dh219/DFB/wiki_resources/dead_socket.jpg

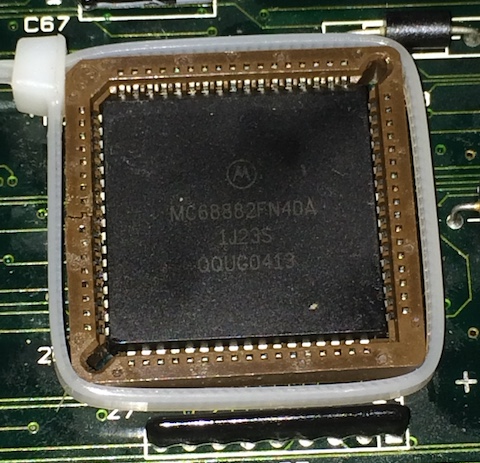
wiki_resources/dead_socket.jpg
