dh219/DFB/wiki_resources/DFB1r3_working.jpeg

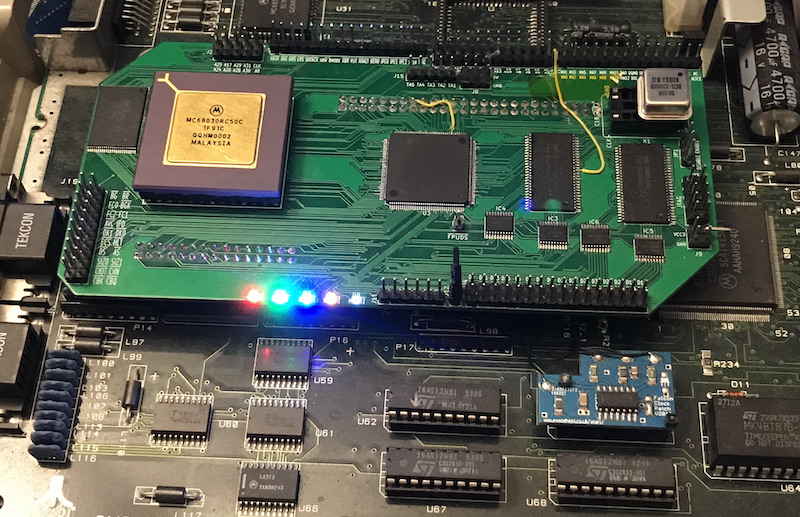
wiki_resources/DFB1r3_working.jpeg
