dh219/DFB/wiki_resources/DFB_memory.png

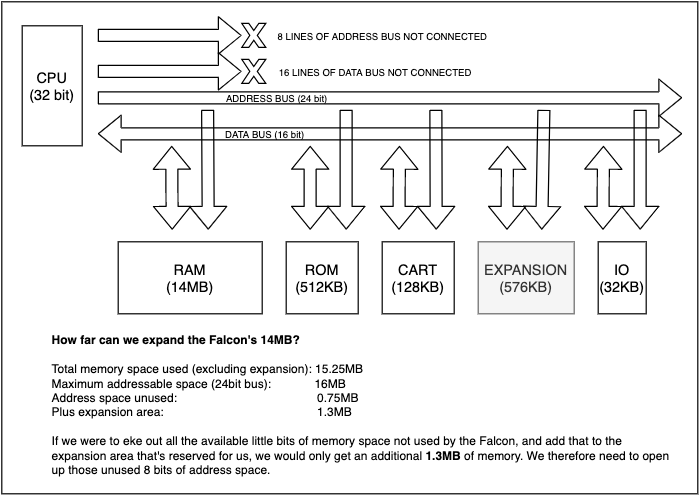
wiki_resources/DFB_memory.png
