dh219/DFB/wiki_resources/diag_cart_signs_of_life.jpeg

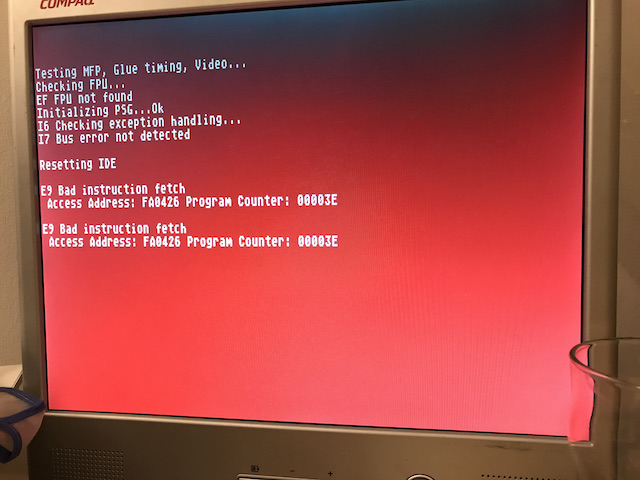
wiki_resources/diag_cart_signs_of_life.jpeg
