dh219/DFB/wiki_resources/DSACK0_stock.jpeg

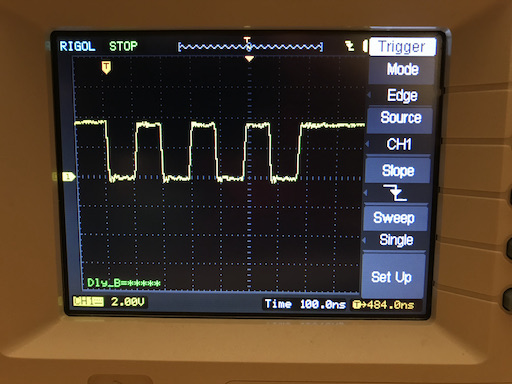
wiki_resources/DSACK0_stock.jpeg
