dh219/DFB/wiki_resources/DSP_access_native.png

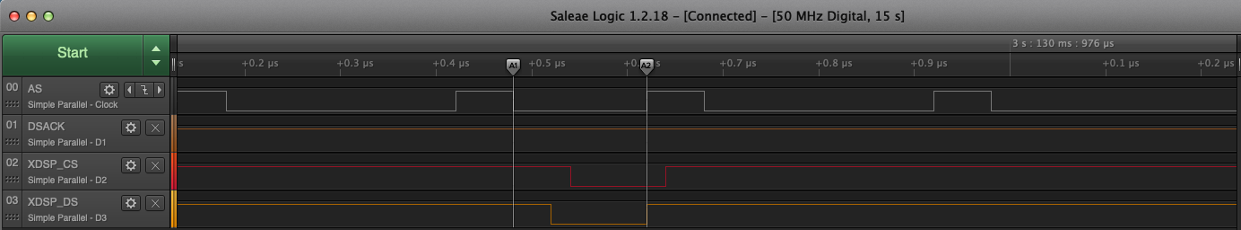
wiki_resources/DSP_access_native.png
