dh219/DFB/wiki_resources/fpu_hack.jpeg

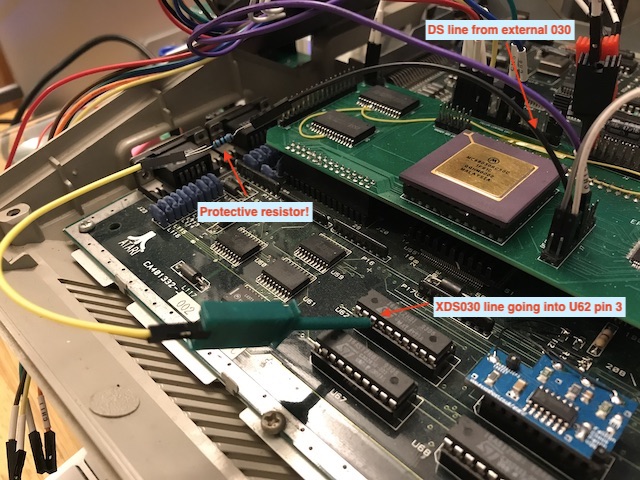
wiki_resources/fpu_hack.jpeg
