dh219/DFB/wiki_resources/rev1.jpeg

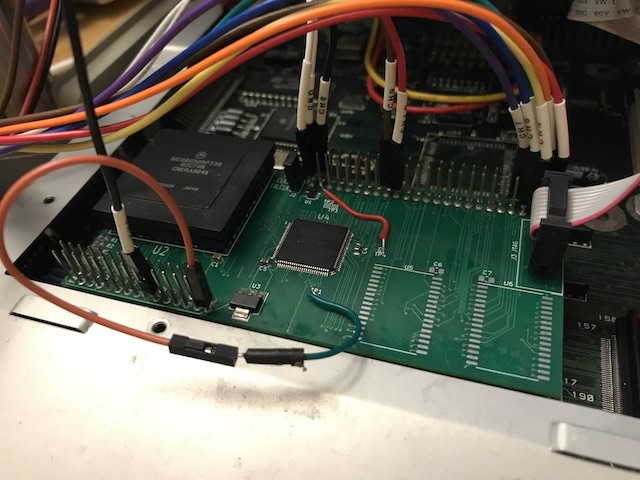
wiki_resources/rev1.jpeg
