dh219/DFB/wiki_resources/rev1_ram.jpeg

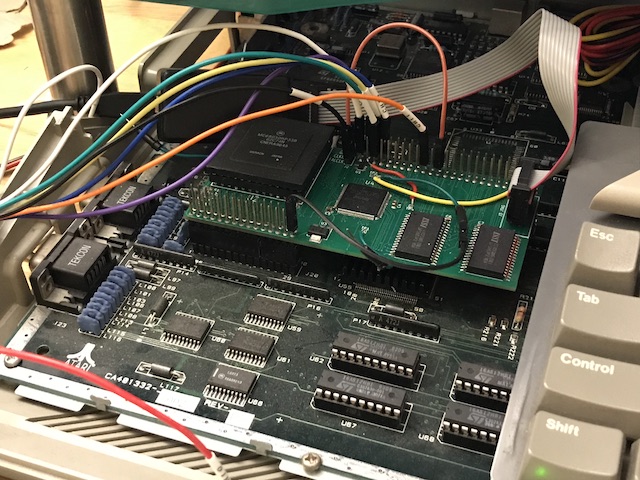
wiki_resources/rev1_ram.jpeg
