dh219/DFB/wiki_resources/rev2.jpeg

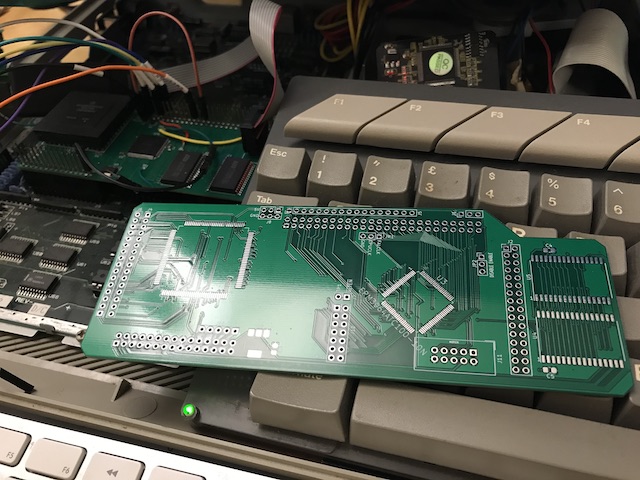
wiki_resources/rev2.jpeg
