dh219/DFB/wiki_resources/rev2b_noram.jpeg

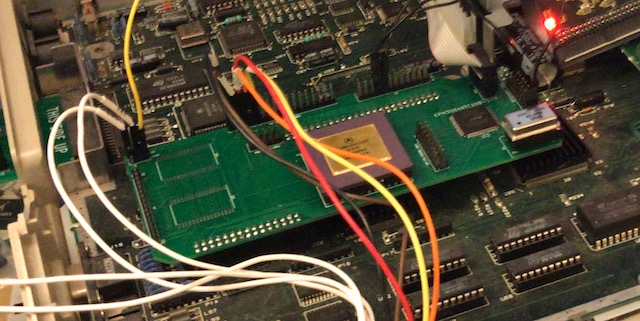
wiki_resources/rev2b_noram.jpeg
