dh219/DFB/wiki_resources/rev2b_ram.jpeg

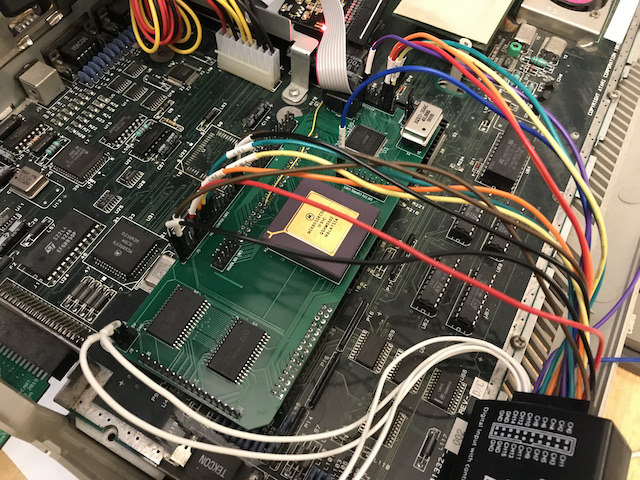
wiki_resources/rev2b_ram.jpeg
