dh219/DFB/wiki_resources/U62.png

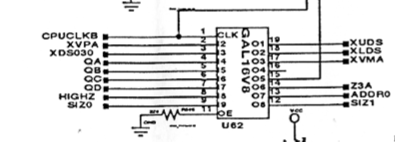
wiki_resources/U62.png
