dh219/DFB/wiki_resources/DSP_access_board_problem.png

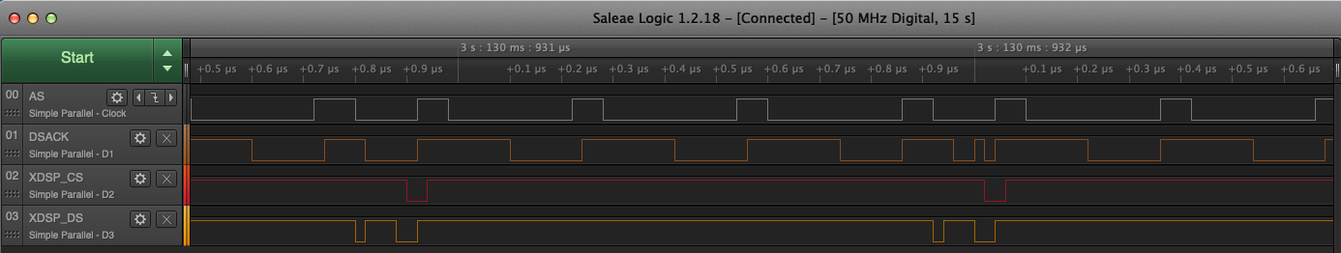
wiki_resources/DSP_access_board_problem.png
