dh219/DFB/DFB1/ise/sdram_defines.v

/*	 sdram_defines.v

	Copyright (c) 2013-2014, Stephen J. Leary
	All rights reserved.

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
	THIS SOFTWARE IS PROVIDED BY THE COPYRIGHT HOLDERS AND CONTRIBUTORS "AS IS" AND
	ANY EXPRESS OR IMPLIED WARRANTIES, INCLUDING, BUT NOT LIMITED TO, THE IMPLIED
	WARRANTIES OF MERCHANTABILITY AND FITNESS FOR A PARTICULAR PURPOSE ARE
	DISCLAIMED. IN NO EVENT SHALL STEPHEN J. LEARY BE LIABLE FOR ANY
	DIRECT, INDIRECT, INCIDENTAL, SPECIAL, EXEMPLARY, OR CONSEQUENTIAL DAMAGES
	(INCLUDING, BUT NOT LIMITED TO, PROCUREMENT OF SUBSTITUTE GOODS OR SERVICES;
	LOSS OF USE, DATA, OR PROFITS; OR BUSINESS INTERRUPTION) HOWEVER CAUSED AND
	ON ANY THEORY OF LIABILITY, WHETHER IN CONTRACT, STRICT LIABILITY, OR TORT
	(INCLUDING NEGLIGENCE OR OTHERWISE) ARISING IN ANY WAY OUT OF THE USE OF THIS
	SOFTWARE, EVEN IF ADVISED OF THE POSSIBILITY OF SUCH DAMAGE. 
*/

localparam RASCAS_DELAY   = 3'd1;   // tRCD=20ns -> 1 cycles@50MHz
localparam BURST_LENGTH   = 3'b000; // 000=1, 001=2, 010=4, 011=8, 111 = continuous.
localparam ACCESS_TYPE    = 1'b0;   // 0=sequential, 1=interleaved
localparam CAS_LATENCY    = 3'd2;   // 2/3 allowed
localparam OP_MODE        = 2'b00;  // only 00 (standard operation) allowed
localparam NO_WRITE_BURST = 1'b1;   // 0= write burst enabled, 1=only single access write
localparam WRITE_BURST 	  = 1'b0;   // 0= write burst enabled, 1=only single access write
localparam RFC_DELAY      = 4'd3;   // tRFC=66ns -> 3 cycles@50MHz

// all possible commands
localparam CMD_INHIBIT         = 4'b1111;
localparam CMD_NOP             = 4'b0111;
localparam CMD_ACTIVE          = 4'b0011;
localparam CMD_READ            = 4'b0101;
localparam CMD_WRITE           = 4'b0100;
localparam CMD_BURST_TERMINATE = 4'b0110;
localparam CMD_PRECHARGE       = 4'b0010;
localparam CMD_AUTO_REFRESH    = 4'b0001;
localparam CMD_LOAD_MODE       = 4'b0000;

// ========================================================
// Convert cmd into ascii name
// ========================================================
function [(12*8)-1:0]  cmd_name;
input [3:0] cmd;
begin
   cmd_name = 
   		   cmd ==  CMD_INHIBIT 			? "CMD_INHIBIT " :
		   cmd ==  CMD_NOP 				? "CMD_NOP     " : 
		   cmd ==  CMD_ACTIVE 			? "CMD_ACTIVE  " : 
		   cmd ==  CMD_READ 			? "CMD_READ    " : 
		   cmd ==  CMD_WRITE 			? "CMD_WRITE   " : 
		   cmd ==  CMD_BURST_TERMINATE 	? "CMD_BRSTTERM" :
		   cmd ==  CMD_PRECHARGE 		? "CMD_PRECHRGE" :
		   cmd ==  CMD_AUTO_REFRESH 	? "CMD_AREFRESH" :
		   cmd ==  CMD_LOAD_MODE        ? "CMD_LOAD_MDE" :
                                          "UNKNOWN     ";
end
endfunction
